jpralves/cseduino/boards/1-layer/cseduinov3-board-back.jpg

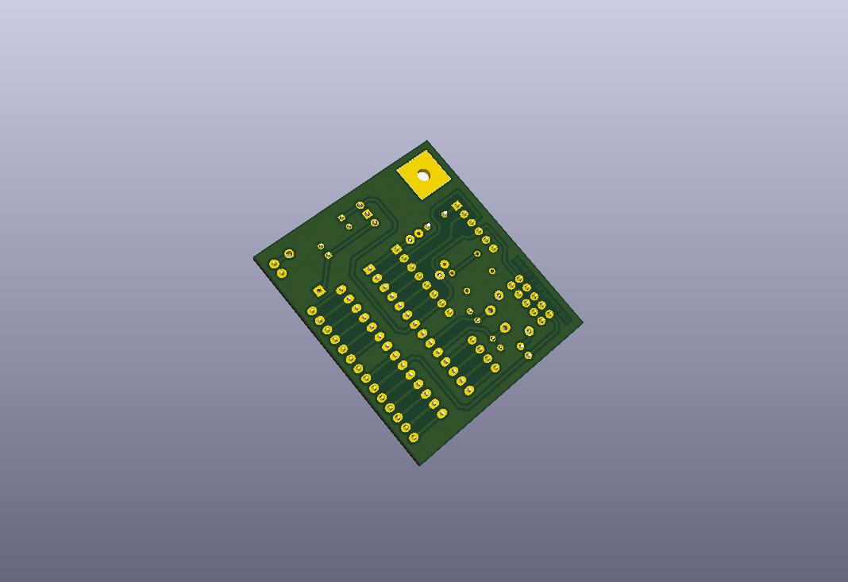
boards/1-layer/cseduinov3-board-back.jpg
