jpralves/cseduino/boards/1-layer/cseduinov3.kicad_pcb.png

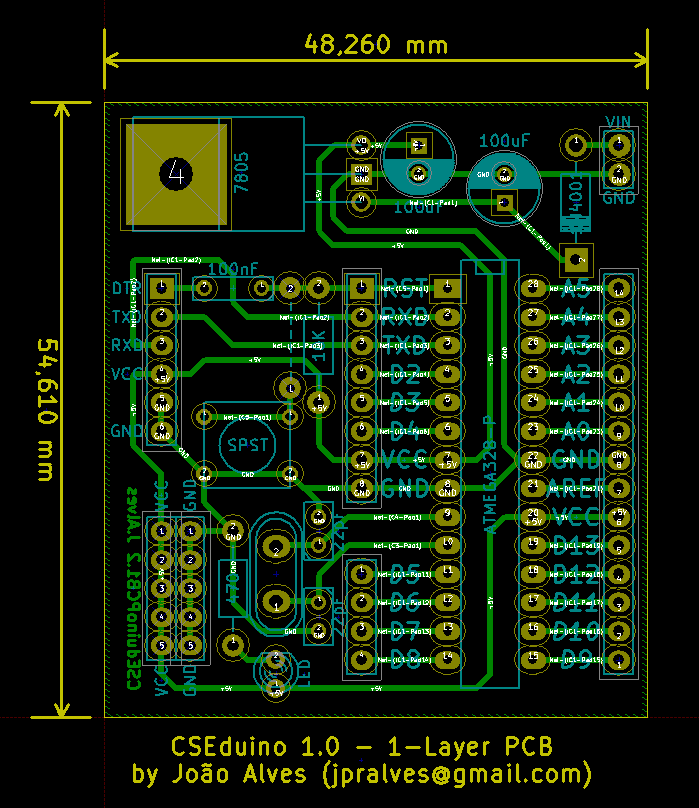
boards/1-layer/cseduinov3.kicad_pcb.png
