jpralves/cseduino/boards/2-layer/cseduinov4.kicad_pcb1.png

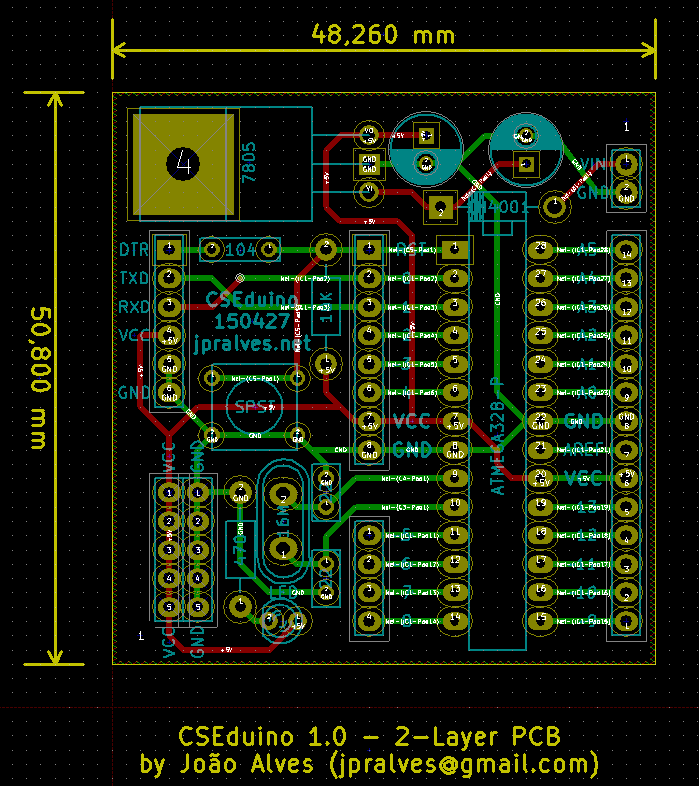
boards/2-layer/cseduinov4.kicad_pcb1.png
