jpralves/cseduino/boards/2-layer/cseduinov4_3d_1.jpg

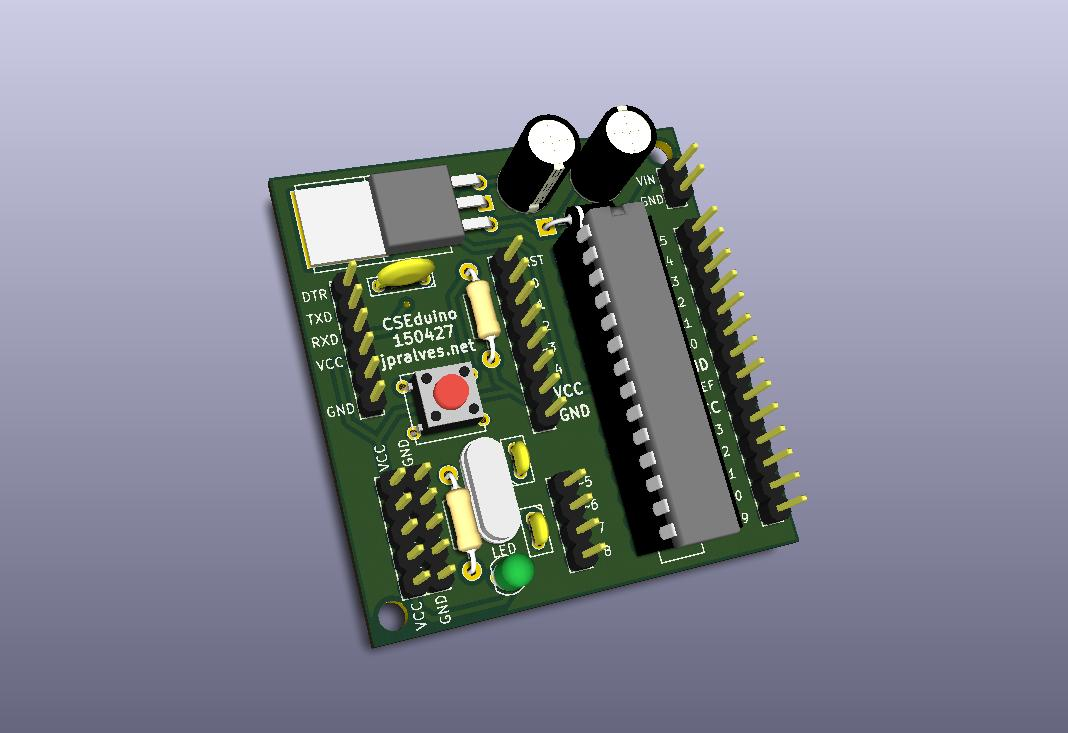
boards/2-layer/cseduinov4_3d_1.jpg
