jpralves/cseduino/workshop/2016-04-02/LedRGB/LedRGB.png

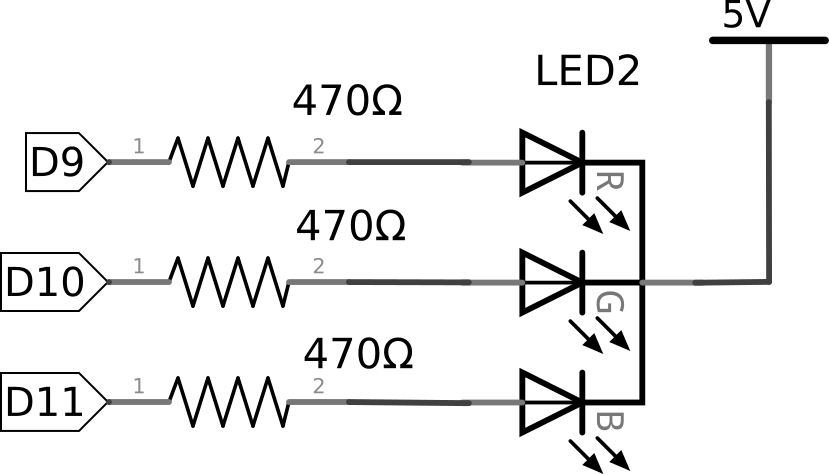
workshop/2016-04-02/LedRGB/LedRGB.png
