jpralves/cseduino/workshop/2016-04-02/Leds/Leds1/Leds1.png

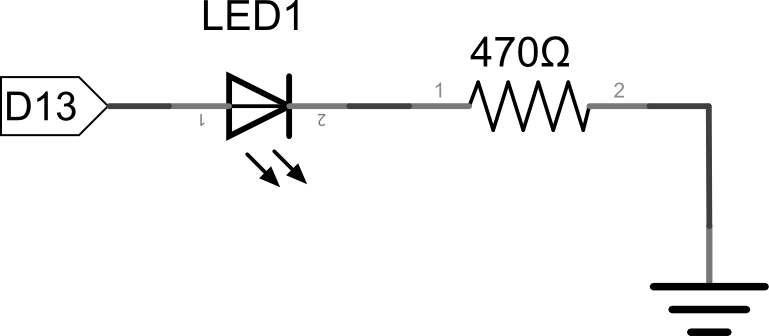
workshop/2016-04-02/Leds/Leds1/Leds1.png
