jpralves/cseduino/workshop/2016-04-02/Theremin/Button.png

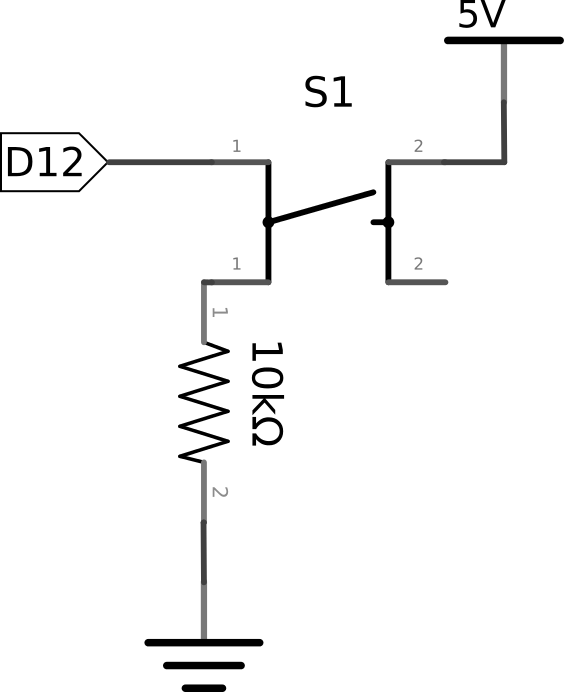
workshop/2016-04-02/Theremin/Button.png
